SwissMaverick/PRJ_2204_Theremin_JJE/doc/V3/Screenshots/Tests ultrasons/Essai 10cm.png

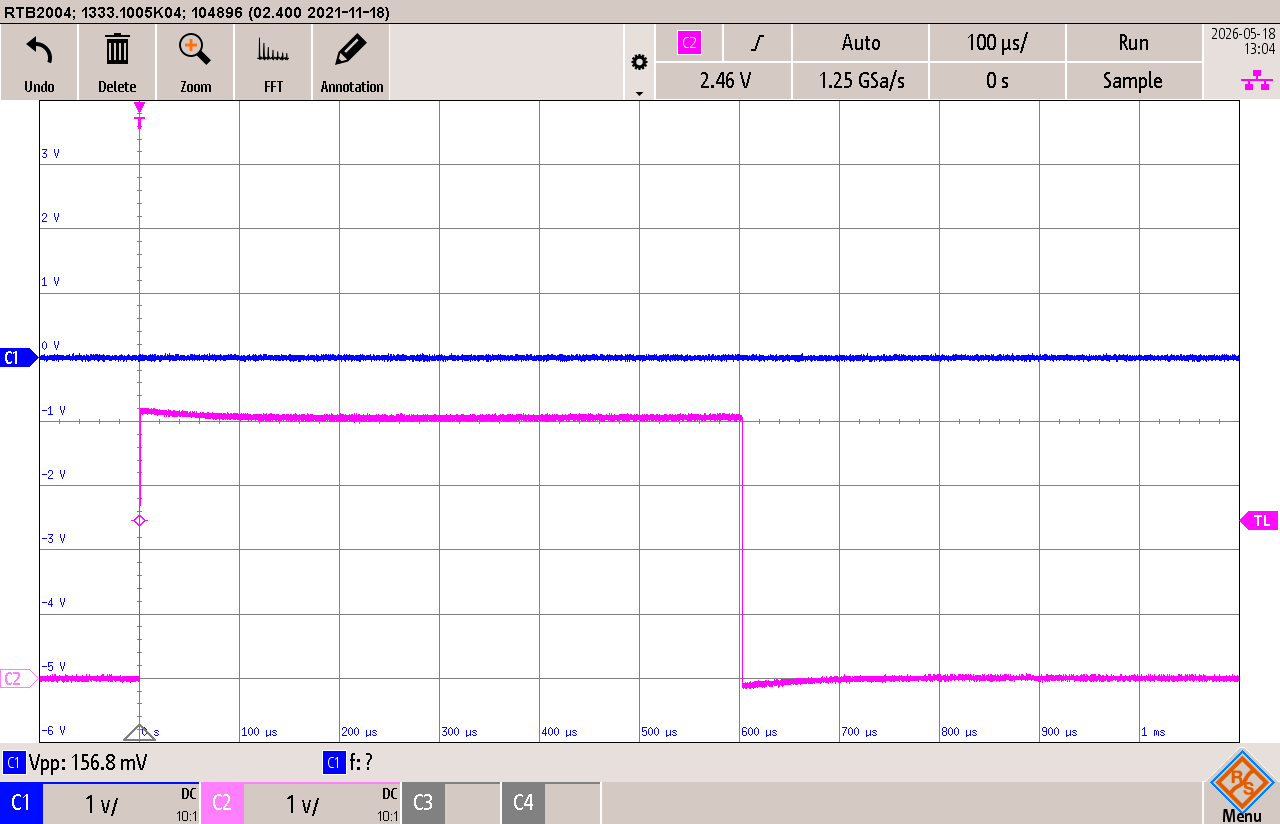
doc/V3/Screenshots/Tests ultrasons/Essai 10cm.png
