SwissMaverick/PRJ_2204_Theremin_JJE/doc/V3/Screenshots/Tests ultrasons/Essai alim 5V (fonctionne).png

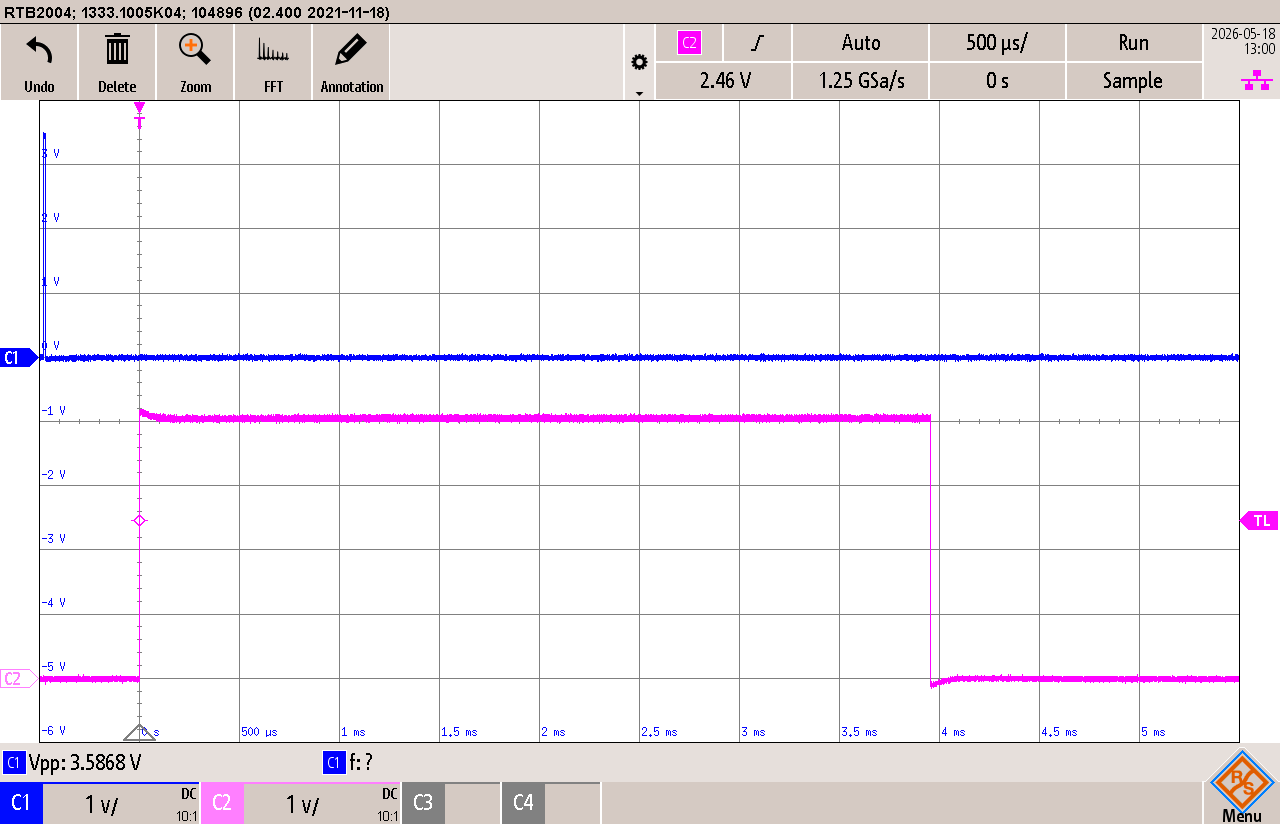
doc/V3/Screenshots/Tests ultrasons/Essai alim 5V (fonctionne).png
