SwissMaverick/PRJ_2204_Theremin_JJE/doc/V3/Screenshots/Tests ultrasons/Premier essai ultrasons (fonctionne pas).png

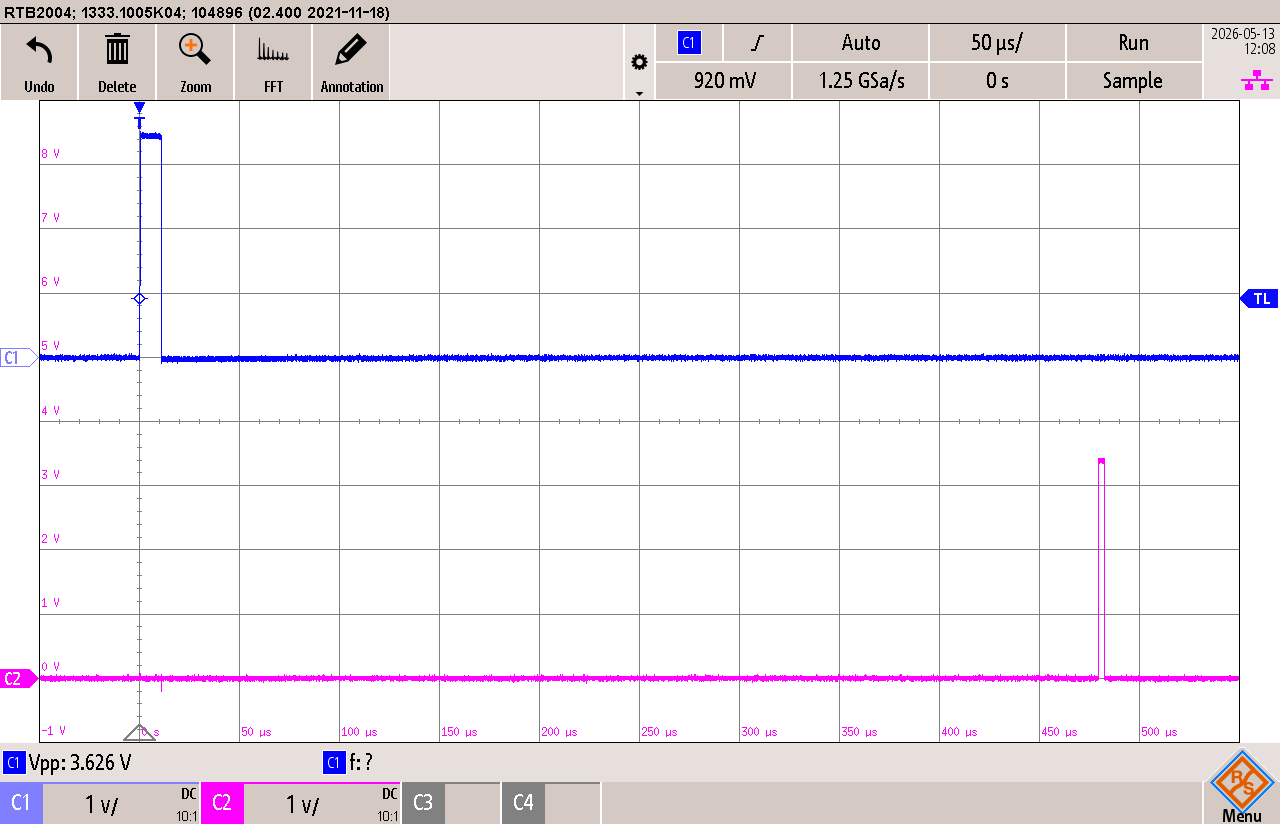
doc/V3/Screenshots/Tests ultrasons/Premier essai ultrasons (fonctionne pas).png
