SwissMaverick/PRJ_2204_Theremin_JJE/Exemple config osci projet POBJ/configuration_bitsSettings.h

//----------------------------------------------------------------------------//
// Nom du projet 		:	Reglage Encodeur
// Nom du fichier 		:   configuration_bitsSettings.h 
// Date de création 	:   02.12.2020
// Date de modification : 	xx.xx.20xx
// 
// Auteur 				: 	Philou (Ph. Bovey) 
//                      :   Kevin Bougnon 
//
// Description 			: 	Canevas pour le laboratoire de réglage avec la carte
//                          1601_HalfBridge 
//                         
// Remarques			: 
// 	    chemin pour trouver le headerfile 
//		C:\Program Files\Microchip\MPLAB C30\support\dsPIC33F\h
//
//      Hardware de la carte ATTENTION PIC MONTER SUR LA CARTE DSPIC33FJ128MC802
//      K:\ES\PROJETS\SLO\1601x_HalfBridge3x\doc 
//
//	    doc pour le DSP : 
//		K:\ES\PROJETS\SLO\1601x_HalfBridge3x\doc\datasheets
// 
//----------------------------------------------------------------------------//
#ifndef CONFIGURATION_BITSSETTINGS_H
#define	CONFIGURATION_BITSSETTINGS_H

//--- librairie à inclure ---// 

// DSPIC33FJ128MC802 Configuration Bit Settings
// 'C' source line config statements

// FBS
#pragma config BWRP = WRPROTECT_OFF     // Boot Segment Write Protect (Boot Segment may be written)
#pragma config BSS = NO_FLASH           // Boot Segment Program Flash Code Protection (No Boot program Flash segment)
#pragma config RBS = NO_RAM             // Boot Segment RAM Protection (No Boot RAM)

// FSS
#pragma config SWRP = WRPROTECT_OFF     // Secure Segment Program Write Protect (Secure segment may be written)
#pragma config SSS = NO_FLASH           // Secure Segment Program Flash Code Protection (No Secure Segment)
#pragma config RSS = NO_RAM             // Secure Segment Data RAM Protection (No Secure RAM)

// FGS
#pragma config GWRP = OFF               // General Code Segment Write Protect (User program memory is not write-protected)
#pragma config GSS = OFF                // General Segment Code Protection (User program memory is not code-protected)

// FOSCSEL
#pragma config FNOSC = FRCPLL           // Oscillator Mode (Internal Fast RC (FRC) w/ PLL)
#pragma config IESO = ON                // Internal External Switch Over Mode (Start-up device with FRC, then automatically switch to user-selected oscillator source when ready)

// FOSC
#pragma config POSCMD = NONE            // Primary Oscillator Source (Primary Oscillator Disabled)
#pragma config OSCIOFNC = OFF           // OSC2 Pin Function (OSC2 pin has clock out function)
#pragma config IOL1WAY = ON             // Peripheral Pin Select Configuration (Allow Only One Re-configuration)
#pragma config FCKSM = CSDCMD           // Clock Switching and Monitor (Both Clock Switching and Fail-Safe Clock Monitor are disabled)

// FWDT
#pragma config WDTPOST = PS32768        // Watchdog Timer Postscaler (1:32,768)
#pragma config WDTPRE = PR128           // WDT Prescaler (1:128)
#pragma config WINDIS = OFF             // Watchdog Timer Window (Watchdog Timer in Non-Window mode)
#pragma config FWDTEN = ON              // Watchdog Timer Enable (Watchdog timer always enabled)

// FPOR
#pragma config FPWRT = PWR128           // POR Timer Value (128ms)  // POR Timer Value (Disabled)
#pragma config ALTI2C = OFF             // Alternate I2C  pins (I2C mapped to SDA1/SCL1 pins)
#pragma config LPOL = ON                // Motor Control PWM Low Side Polarity bit (PWM module low side output pins have active-high output polarity)
#pragma config HPOL = ON                // Motor Control PWM High Side Polarity bit (PWM module high side output pins have active-high output polarity)
#pragma config PWMPIN = ON              // Motor Control PWM Module Pin Mode bit (PWM module pins controlled by PORT register at device Reset)

// FICD
#pragma config ICS = PGD1               // Comm Channel Select (Communicate on PGC1/EMUC1 and PGD1/EMUD1)
#pragma config JTAGEN = OFF             // JTAG Port Enable (JTAG is Disabled)


#endif	/* CONFIGURATION_BITSSETTINGS_H */
